ngc6589/TL866II-PLUS-25V-21V-Adapter/Materials/2716.jpg

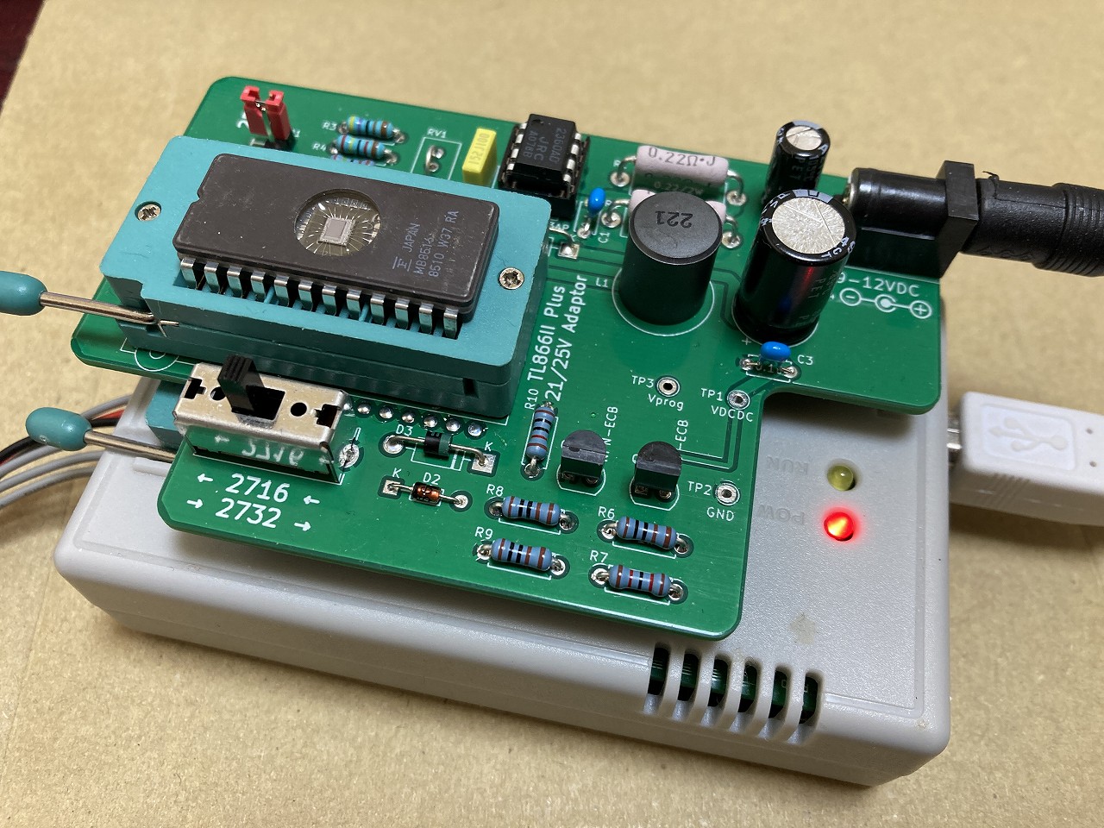
Materials/2716.jpg
