ngc6589/TL866II-PLUS-25V-21V-Adapter/Materials/photo1.jpg

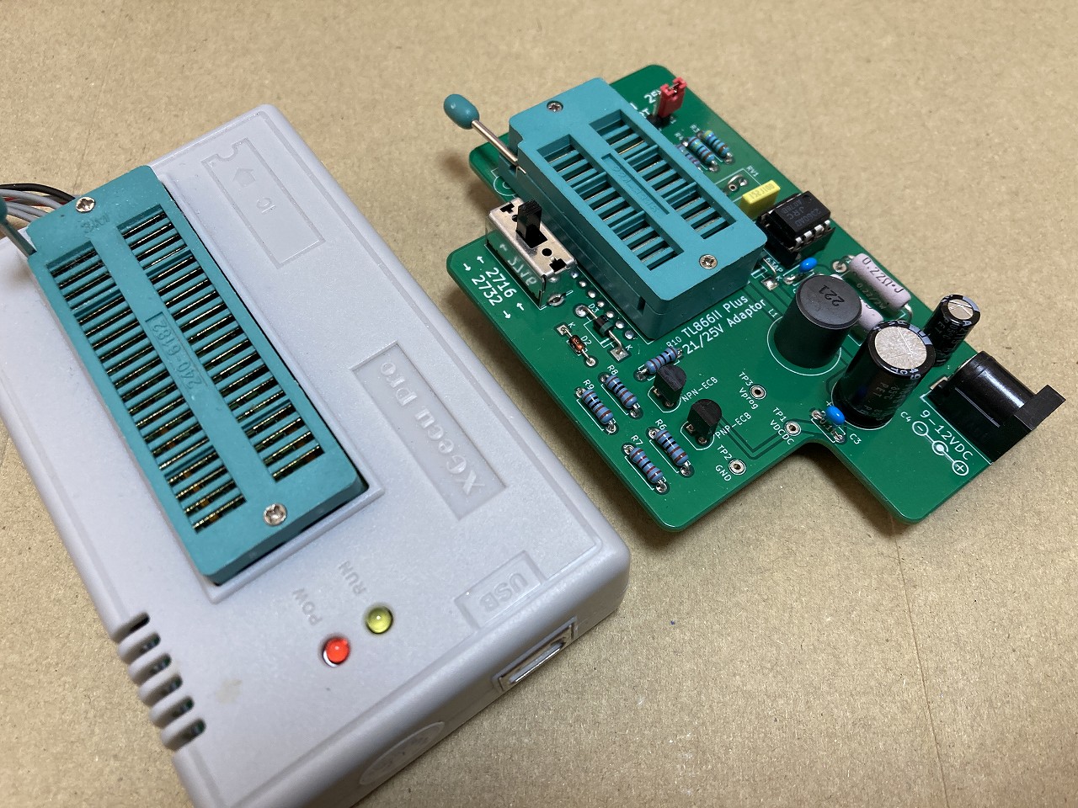
Materials/photo1.jpg
