ngc6589/TL866II-PLUS-25V-21V-Adapter/Materials/photo2.jpg

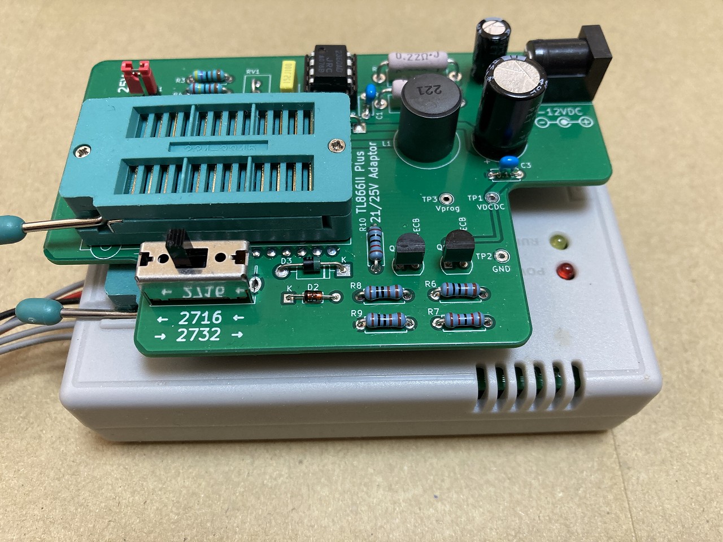
Materials/photo2.jpg
